taladiab8-del/IOT_REPO_SMART_CHAIR/code/arduino_code/chair_predict/dataset.h

#pragma once

#define N_SAMPLES 150
#define N_FEATURES 11

const float FEATURE_MEAN[N_FEATURES] = {
  -0.020557f, 0.010361f, -0.016276f, 0.020638f, 0.005837f, 0.189207f, 0.196955f, 0.193724f, 0.198453f, 0.221591f, 0.052138f
};

const float FEATURE_STD[N_FEATURES] = {
  0.029554f, 0.037725f, 0.031656f, 0.039427f, 0.050282f, 0.030682f, 0.036865f, 0.031860f, 0.038849f, 0.049147f, 0.067571f
};

const float TRAIN_SAMPLES[N_SAMPLES][N_FEATURES] = {
  {0.695584f, -0.274643f, 0.514156f, -0.523455f, -0.116094f, 0.683238f, -0.032333f, 0.696604f, 0.169567f, -0.988067f, -0.771607f},
  {-0.494283f, 0.620530f, 0.401116f, -0.555990f, 0.008306f, -0.462855f, 0.883715f, 0.584289f, 0.136549f, -0.860794f, -0.857737f},
  {-0.957901f, -0.589989f, -0.197509f, 0.185391f, 0.984706f, -0.909416f, -0.355031f, -0.010498f, 0.888958f, 0.138160f, 0.697516f},
  {0.037653f, -1.328001f, -0.215446f, -1.509856f, 2.293806f, 0.049511f, -1.110253f, -0.028320f, -0.831505f, 1.477499f, 0.390705f},
  {-0.545335f, 1.593311f, -1.218759f, 1.028558f, -0.913920f, -0.512028f, 1.879178f, -1.025201f, 1.744666f, -1.804322f, 1.869344f},
  {0.648692f, -0.687087f, 0.513433f, -1.126402f, 0.694228f, 0.638071f, -0.454394f, 0.695886f, -0.442348f, -0.159027f, 0.060557f},
  {0.695584f, -0.274643f, 0.514156f, -0.523455f, -0.116094f, 0.829254f, -0.075780f, 0.617987f, -0.487926f, -0.475927f, -0.771607f},
  {2.337819f, -0.496455f, -0.943473f, -1.366650f, 0.664185f, 2.411071f, -0.302764f, -0.830296f, -1.343662f, 0.322376f, 1.892769f},
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
  {-0.304132f, -0.733281f, 1.306066f, 0.431362f, -0.431582f, -0.769253f, -1.052521f, 1.288090f, 0.038826f, 0.404063f, 0.030383f},
  {0.530044f, -0.770776f, -0.022692f, -0.209312f, 0.445136f, 0.034233f, -1.090890f, -0.032148f, -0.611377f, 1.301033f, -0.273490f},
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
};

const int TRAIN_LABELS[N_SAMPLES] = {
  1, 2, 3, 4, 5, 6, 1, 2, 3, 4, 5, 6, 1, 2, 3, 4, 5, 6, 1, 2, 3, 4, 5, 6, 1, 2, 3, 4, 5, 6, 1, 2, 3, 4, 5, 6, 1, 2, 3, 4, 5, 6, 1, 2, 3, 4, 5, 6, 1, 2, 3, 4, 5, 6, 1, 2, 3, 4, 5, 6, 1, 2, 3, 4, 5, 6, 1, 2, 3, 4, 5, 6, 1, 2, 3, 4, 5, 6, 1, 2, 3, 4, 5, 6, 1, 2, 3, 4, 5, 6, 1, 2, 3, 4, 5, 6, 1, 2, 3, 4, 5, 6, 1, 2, 3, 4, 5, 6, 1, 2, 3, 4, 5, 6, 1, 2, 3, 4, 5, 6, 1, 2, 3, 4, 5, 6, 1, 2, 3, 4, 5, 6, 1, 2, 3, 4, 5, 6, 1, 2, 3, 4, 5, 6, 1, 2, 3, 4, 5, 6
};
