taladiab8-del/IOT_REPO_SMART_CHAIR/Unit Tests/ON_OFF_Button/ON_OFF_Button.ino

const int switchPin =18;  // ON/OFF toggle switch pin
int switchState = 0;

void setup() {
  Serial.begin(9600);
  pinMode(switchPin, INPUT_PULLDOWN); 
}

void loop() {
  switchState = digitalRead(switchPin);

  if (switchState == HIGH) {
    Serial.println("Switch is ON");
  } else {
    Serial.println("Switch is OFF");
  }

  delay(300);
}
