taladiab8-del/IOT_REPO_SMART_CHAIR/Unit Tests/pressure_sensor/pressure_sensor.ino

const int analogInPin = 34;  // Analog input pin that the potentiometer is attached to

int sensorValue = 0;  // value read from the pot

void setup() {
  // initialize serial communications at 9600 bps:
  Serial.begin(9600);
}

void loop() {
  // read the analog in value:
  sensorValue = analogRead(analogInPin);

  // print the results to the Serial Monitor:
  Serial.print("sensor = ");
  Serial.print(sensorValue);
  delay(4);
}
